Ratlike/SimPedalsESP32/LoadCell.h

// LoadCell.h
#pragma once
#include <ADS1256.h> 
#include <stdint.h>

#include "Main.h"

extern volatile float g_lastBrakeKg;
extern ADS1256& ADC();

class LoadCell_ADS1256
{
private:
  float _zeroPoint = 0.0;
  float _varianceEstimate = 0.0;
  float _standardDeviationEstimate = 0.0;

public:
  LoadCell_ADS1256(uint8_t channel0 = 1, uint8_t channel1 = 0);
  float getReadingKg() const;
  // float getAngleMeasurement() const;
  void setLoadcellRating(uint8_t loadcellRating_u8) const;

public:
  void setZeroPoint();
  void estimateVariance();

public:
  float getVarianceEstimate() const
  {
    return _varianceEstimate;
  }
};
